ailifelab/cyberpunk-mask/CyberpunkMaskEsp32/image_action_forward.h

#define image_forward_width 50
#define image_forward_height 60
const uint8_t image_forward_bits[] PROGMEM = {
  0x00, 0x00, 0x00, 0x00, 0x00, 0x00, 0x00, 0x00, 0x00, 0x00, 0x00, 0x00,
  0x00, 0x00, 0x00, 0x00, 0x00, 0x00, 0x00, 0x00, 0x00, 0x00, 0x00, 0x00,
  0x00, 0x00, 0x00, 0x00, 0x00, 0x00, 0x00, 0x00, 0x00, 0x00, 0x00, 0x00,
  0x00, 0x00, 0x7C, 0x00, 0x00, 0x00, 0x00, 0x00, 0x00, 0xFF, 0x00, 0x00,
  0x00, 0x00, 0x00, 0x00, 0xFF, 0x01, 0x00, 0x00, 0x00, 0x00, 0x00, 0xFF,
  0x01, 0x00, 0x00, 0x00, 0x00, 0x80, 0xFF, 0x01, 0x00, 0x00, 0x00, 0x00,
  0x80, 0xFF, 0x01, 0x00, 0x00, 0x00, 0x00, 0x80, 0xFF, 0x01, 0x00, 0x00,
  0x00, 0x00, 0x00, 0xFF, 0x01, 0x00, 0x00, 0x00, 0x00, 0x00, 0xFE, 0x38,
  0x00, 0x00, 0x00, 0x00, 0x00, 0x3E, 0x38, 0x00, 0x00, 0x00, 0x00, 0xC0,
  0x1F, 0x3C, 0x00, 0x00, 0x00, 0x00, 0xF8, 0x1F, 0x3C, 0x00, 0x00, 0x00,
  0x00, 0xFE, 0x3F, 0x1E, 0x00, 0x00, 0x00, 0x00, 0x7F, 0x7F, 0x1E, 0x00,
  0x00, 0x00, 0x00, 0x1F, 0x7E, 0x0F, 0x00, 0x00, 0x00, 0x80, 0x07, 0xFE,
  0x0F, 0x00, 0x00, 0x00, 0x80, 0x07, 0xFF, 0x07, 0x00, 0x00, 0x00, 0x80,
  0x03, 0xEF, 0x07, 0x00, 0x00, 0x00, 0x80, 0x07, 0xC7, 0x03, 0x00, 0x00,
  0x00, 0x80, 0x03, 0xC7, 0x03, 0x00, 0x00, 0x00, 0x80, 0x03, 0x07, 0x01,
  0x00, 0x00, 0x00, 0xC0, 0x03, 0x07, 0x00, 0x00, 0x00, 0x00, 0xC0, 0x03,
  0x07, 0x00, 0x00, 0x00, 0x00, 0xC0, 0x01, 0x07, 0x00, 0x00, 0x00, 0x00,
  0xC0, 0x81, 0x07, 0x00, 0x00, 0x00, 0x00, 0xC0, 0x81, 0x07, 0x00, 0x00,
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
  0x00, 0x00, 0xE0, 0x03, 0x00, 0x00, 0x00, 0x00, 0x00, 0xC0, 0x07, 0x00,
  0x00, 0x00, 0x00, 0x00, 0x80, 0x07, 0x00, 0x00, 0x00, 0x00, 0x00, 0x00,
  0x03, 0x00, 0x00, 0x00, 0x00, 0x00, 0x00, 0x00, 0x00, 0x00, 0x00, 0x00,
};
