ailifelab/cyberpunk-mask/CyberpunkMaskEsp32/image_action_cube.h

#define image_cube_width 55
#define image_cube_height 60
const uint8_t  image_cube_bits[] PROGMEM = {
  0x00, 0x00, 0x00, 0x00, 0x00, 0x00, 0x00, 0x00, 0x00, 0x00, 0x00, 0x00,
  0x00, 0x00, 0x00, 0x00, 0x00, 0x10, 0x00, 0x00, 0x00, 0x00, 0x00, 0x00,
  0xF8, 0x00, 0x00, 0x00, 0x00, 0x00, 0x00, 0xFE, 0x01, 0x00, 0x00, 0x00,
  0x00, 0xE0, 0xDF, 0x07, 0x00, 0x00, 0x00, 0x00, 0xFC, 0x03, 0x1F, 0x00,
  0x00, 0x00, 0x00, 0x3F, 0x00, 0xFC, 0x00, 0x00, 0x00, 0xE0, 0x07, 0x00,
  0xF0, 0x03, 0x00, 0x00, 0xF8, 0x01, 0x00, 0x80, 0x0F, 0x00, 0x00, 0x3F,
  0x00, 0x00, 0x00, 0x3E, 0x00, 0xFC, 0x07, 0x00, 0x00, 0x00, 0xF8, 0x01,
  0xFC, 0x00, 0x00, 0x00, 0x00, 0xC0, 0x1F, 0x3C, 0x00, 0x00, 0x00, 0x00,
  0x00, 0x1F, 0x7C, 0x00, 0x00, 0x00, 0x00, 0xC0, 0x1F, 0xEC, 0x01, 0x00,
  0x00, 0x00, 0xF0, 0x19, 0x8C, 0x07, 0x00, 0x00, 0x00, 0x7C, 0x18, 0x0C,
  0x1E, 0x00, 0x00, 0x00, 0x1E, 0x18, 0x0C, 0x7C, 0x00, 0x00, 0x80, 0x03,
  0x18, 0x0C, 0xF0, 0x07, 0x00, 0xE0, 0x01, 0x18, 0x0C, 0xC0, 0x1F, 0x00,
  0x7C, 0x00, 0x18, 0x0C, 0x00, 0x3C, 0x00, 0x1F, 0x00, 0x18, 0x0C, 0x00,
  0xF0, 0xF0, 0x07, 0x00, 0x18, 0x0C, 0x00, 0xC0, 0xFF, 0x00, 0x00, 0x18,
  0x0C, 0x00, 0x80, 0x1F, 0x00, 0x00, 0x1C, 0x0C, 0x00, 0x00, 0x03, 0x00,
  0x00, 0x0C, 0x18, 0x00, 0x00, 0x03, 0x00, 0x00, 0x0C, 0x18, 0x00, 0x00,
  0x03, 0x00, 0x00, 0x0C, 0x18, 0x00, 0x00, 0x03, 0x00, 0x00, 0x0C, 0x18,
  0x00, 0x00, 0x03, 0x00, 0x00, 0x0C, 0x18, 0x00, 0x00, 0x03, 0x00, 0x00,
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
  0x00, 0xC0, 0x00, 0x00, 0x00, 0x18, 0x70, 0x00, 0xC0, 0x00, 0x00, 0x00,
  0x18, 0xE0, 0x00, 0xC0, 0x00, 0x00, 0x00, 0x0C, 0xC0, 0x01, 0xC0, 0x00,
  0x00, 0x00, 0x0C, 0x00, 0x07, 0xC0, 0x00, 0x00, 0x00, 0x0F, 0x00, 0x0E,
  0xC0, 0x00, 0x00, 0x80, 0x0F, 0x00, 0x1C, 0xC0, 0x00, 0x00, 0xE0, 0x01,
  0x00, 0x38, 0xC0, 0x00, 0x00, 0xF8, 0x00, 0x00, 0x70, 0xC0, 0x00, 0x00,
  0x3E, 0x00, 0x00, 0xE0, 0xC1, 0x00, 0xC0, 0x0F, 0x00, 0x00, 0xC0, 0xC7,
  0x00, 0xF0, 0x03, 0x00, 0x00, 0x00, 0xCF, 0x01, 0x7C, 0x00, 0x00, 0x00,
  0x00, 0xFC, 0xC1, 0x1F, 0x00, 0x00, 0x00, 0x00, 0xF0, 0xF1, 0x07, 0x00,
  0x00, 0x00, 0x00, 0xE0, 0x7F, 0x00, 0x00, 0x00, 0x00, 0x00, 0x80, 0x1F,
  0x00, 0x00, 0x00, 0x00, 0x00, 0x80, 0x03, 0x00, 0x00, 0x00, 0x00, 0x00,
  0x00, 0x00, 0x00, 0x00, 0x00, 0x00, 0x00, 0x00, 0x00, 0x00, 0x00, 0x00,
};
