ailifelab/cyberpunk-mask/CyberpunkMaskEsp32/image_action_cube_long.h

#define cube_long_width 84
#define cube_long_height 56
const uint8_t cube_long_bits[] PROGMEM = {
  0x00, 0x00, 0x00, 0x00, 0x00, 0x00, 0x00, 0x00, 0x00, 0x00, 0x00, 0x00,
  0x00, 0x00, 0x00, 0x00, 0x00, 0xF8, 0x01, 0x00, 0x00, 0x00, 0x00, 0x00,
  0x00, 0x00, 0x00, 0x00, 0x07, 0x1E, 0x00, 0x00, 0x00, 0x00, 0x00, 0x00,
  0x00, 0x00, 0xE0, 0x00, 0xE0, 0x00, 0x00, 0x00, 0x00, 0x00, 0x00, 0x00,
  0x00, 0x1C, 0x00, 0x00, 0x07, 0x00, 0x00, 0x00, 0x00, 0x00, 0x00, 0x00,
  0x03, 0x00, 0x00, 0x78, 0x00, 0x00, 0x00, 0x00, 0x00, 0x00, 0xE0, 0x00,
  0x00, 0x00, 0x80, 0x03, 0x00, 0x00, 0x00, 0x00, 0x00, 0x1C, 0x00, 0x00,
  0x00, 0x00, 0x1C, 0x00, 0x00, 0x00, 0x00, 0x80, 0x03, 0x00, 0x00, 0x00,
  0x00, 0xE0, 0x01, 0x00, 0x00, 0x00, 0x70, 0x00, 0x00, 0x00, 0x00, 0x00,
  0x00, 0x0E, 0x00, 0x00, 0x00, 0x3E, 0x00, 0x00, 0x00, 0x00, 0x00, 0x00,
  0x0F, 0x00, 0x00, 0x80, 0xC9, 0x01, 0x00, 0x00, 0x00, 0x00, 0xE0, 0x08,
  0x00, 0x00, 0x70, 0x08, 0x0E, 0x00, 0x00, 0x00, 0x00, 0x18, 0x08, 0x00,
  0x00, 0x0E, 0x08, 0xF0, 0x00, 0x00, 0x00, 0x00, 0x07, 0x0C, 0x00, 0xC0,
  0x01, 0x08, 0x00, 0x07, 0x00, 0x00, 0xE0, 0x00, 0x08, 0x00, 0x38, 0x00,
  0x08, 0x00, 0x78, 0x00, 0x00, 0x1C, 0x00, 0x08, 0x00, 0x07, 0x00, 0x08,
  0x00, 0x80, 0x03, 0x80, 0x03, 0x00, 0x08, 0xC0, 0x00, 0x00, 0x08, 0x00,
  0x00, 0x1C, 0xE0, 0x00, 0x00, 0x08, 0x38, 0x00, 0x00, 0x08, 0x00, 0x00,
  0xE0, 0x1E, 0x00, 0x00, 0x0C, 0x06, 0x00, 0x00, 0x0C, 0x00, 0x00, 0x00,
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
  0x00, 0x80, 0x0F, 0x88, 0x01, 0x00, 0x00, 0x04, 0xC0, 0x00, 0x00, 0x00,
  0x00, 0xF0, 0xE8, 0x00, 0x00, 0x00, 0x06, 0x30, 0x00, 0x00, 0x00, 0x00,
  0x00, 0x1F, 0x00, 0x00, 0x00, 0x04, 0x0C, 0x00, 0x00, 0x00, 0x00, 0x00,
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
};
