ailifelab/cyberpunk-mask/CyberpunkMaskEsp32/images.h

#define WiFi_Logo_width 60
#define WiFi_Logo_height 36
const uint8_t WiFi_Logo_bits[] PROGMEM = {
  0x00, 0x00, 0x00, 0x00, 0x00, 0x00, 0x00, 0x00, 0x00, 0x00, 0x00, 0xF8,
  0x00, 0x00, 0x00, 0x00, 0x00, 0x00, 0x80, 0xFF, 0x07, 0x00, 0x00, 0x00,
  0x00, 0x00, 0xE0, 0xFF, 0x1F, 0x00, 0x00, 0x00, 0x00, 0x00, 0xF8, 0xFF,
  0x7F, 0x00, 0x00, 0x00, 0x00, 0x00, 0xFC, 0xFF, 0xFF, 0x00, 0x00, 0x00,
  0x00, 0x00, 0xFE, 0xFF, 0xFF, 0x01, 0x00, 0x00, 0x00, 0x00, 0xFF, 0xFF,
  0xFF, 0x03, 0x00, 0x00, 0x00, 0xFC, 0xFF, 0xFF, 0xFF, 0xFF, 0x00, 0x00,
  0x00, 0xFF, 0xFF, 0xFF, 0x07, 0xC0, 0x83, 0x01, 0x80, 0xFF, 0xFF, 0xFF,
  0x01, 0x00, 0x07, 0x00, 0xC0, 0xFF, 0xFF, 0xFF, 0x00, 0x00, 0x0C, 0x00,
  0xC0, 0xFF, 0xFF, 0x7C, 0x00, 0x60, 0x0C, 0x00, 0xC0, 0x31, 0x46, 0x7C,
  0xFC, 0x77, 0x08, 0x00, 0xE0, 0x23, 0xC6, 0x3C, 0xFC, 0x67, 0x18, 0x00,
  0xE0, 0x23, 0xE4, 0x3F, 0x1C, 0x00, 0x18, 0x00, 0xE0, 0x23, 0x60, 0x3C,
  0x1C, 0x70, 0x18, 0x00, 0xE0, 0x03, 0x60, 0x3C, 0x1C, 0x70, 0x18, 0x00,
  0xE0, 0x07, 0x60, 0x3C, 0xFC, 0x73, 0x18, 0x00, 0xE0, 0x87, 0x70, 0x3C,
  0xFC, 0x73, 0x18, 0x00, 0xE0, 0x87, 0x70, 0x3C, 0x1C, 0x70, 0x18, 0x00,
  0xE0, 0x87, 0x70, 0x3C, 0x1C, 0x70, 0x18, 0x00, 0xE0, 0x8F, 0x71, 0x3C,
  0x1C, 0x70, 0x18, 0x00, 0xC0, 0xFF, 0xFF, 0x3F, 0x00, 0x00, 0x08, 0x00,
  0xC0, 0xFF, 0xFF, 0x1F, 0x00, 0x00, 0x0C, 0x00, 0x80, 0xFF, 0xFF, 0x1F,
  0x00, 0x00, 0x06, 0x00, 0x80, 0xFF, 0xFF, 0x0F, 0x00, 0x00, 0x07, 0x00,
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
  0xFC, 0xFB, 0xDF, 0xFE, 0xF9, 0x9F, 0xEF, 0xFE, 0xF3, 0xAF, 0xFC, 0xF9,
  0x9F, 0xC7, 0x00, 0xFB, 0x00, 0xF1, 0xF9, 0x9F, 0xE3, 0x00, 0xF3, 0x00,
  0xE3, 0xFD, 0x9F, 0xF8, 0x00, 0xFB, 0x00, 0x8F, 0xF9, 0xEF, 0xFE, 0x00,
  0xF3, 0x00, 0xDF, 0xF9, 0xDF, 0x00, 0x00, 0xFB, 0x00, 0xAF, 0xF8, 0xAF,
  0xFC, 0x00, 0xF3, 0x00, 0x00, 0xF8, 0x00, 0xF8, 0x00, 0xFB, 0x00, 0xDF,
  0xFE, 0x00, 0xE3, 0x00, 0xF3, 0x00, 0x8F, 0x00, 0x00, 0xCF, 0x00, 0xF3,
  0x00, 0xC3, 0x00, 0x00, 0xEF, 0x00, 0xFB, 0x00, 0xF8, 0x00, 0x00, 0xAF,
  0xFE, 0xF3, 0xAF, 0xFC, 0x00, 0x00, 0x00, 0xF8, 0xFB, 0x0F, 0x00, 0x00,
  0x00, 0x00, 0xE3, 0xFB, 0xC7, 0x00, 0x00, 0x00, 0x00, 0xCF, 0xF3, 0xF1,
  0x00, 0x00, 0x00, 0x00, 0xEF, 0xA3, 0xFC, 0x00, 0x00, 0x00, 0x00, 0xDF,
  0xE2, 0x00, 0x00, 0x00, 0x00, 0x00, 0x00, 0xC0, 0x00, 0x00, 0x00, 0x00,
  0x00, 0x00, 0xF3, 0x00, 0x00, 0x00, 0x00, 0x00, 0x00, 0x00, 0x00, 0x00,
  0x00, 0x00, 0x00, 0x00, 0x00, 0x00, 0x00, 0x00,
};

const uint8_t activeSymbol[] PROGMEM = {
  B00000000,
  B00000000,
  B00011000,
  B00100100,
  B01000010,
  B01000010,
  B00100100,
  B00011000
};

const uint8_t inactiveSymbol[] PROGMEM = {
  B00000000,
  B00000000,
  B00000000,
  B00000000,
  B00011000,
  B00011000,
  B00000000,
  B00000000
};
